JamesNZL/algovision/docs/Scopes/Power/Buck Converter.md

#5e5ce6/projects 

# Buck Converter

- Do I even need a buck converter, or should I just use a [[Low Dropout Regulator]]? I'm only going from $5\,\text{V}\to3.3\,\text{V}$...

- [Buck Regulators - Products (st.com)](https://www.st.com/en/power-management/buck-regulators/products.html)
- [Buck converters (integrated switch) product selection | TI.com](https://www.ti.com/power-management/non-isolated-dc-dc-switching-regulators/step-down-buck/buck-converter-integrated-switch/products.html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)
