JamesNZL/algovision/docs/Scopes/Software/Altium.md

#5e5ce6/projects 

# Altium Designer

- Used for the hardware schematic capture and PCB artwork design.

> [!note]
> I have also created my own schematic template with a custom title block.

![[Pasted image 20231009000126.png]]

![[Pasted image 20231120011738.png]]

![[Pasted image 20231120011808.png]]

![[Pasted image 20231009000355.png]]

![[Pasted image 20231009000413.png]]
