JamesNZL/algovision/docs/Scopes/Interface/User Pushbuttons.md

#5e5ce6/projects 

# User Pushbuttons

- [[Scopes/Interface/Reset Button]]

Also see [[Operating Modes]]
