JamesNZL/algovision/docs/Scopes/Power/Power Indicator.md

#5e5ce6/projects 

# Power Indicator

I want a power indication LED that can also communicate whether [[USB Power Delivery]] negotiation was successful.
