JamesNZL/algovision/docs/Scopes/Power/Input Protection.md

#5e5ce6/projects 

# Input Protection

> [!todo]
> https://www.st.com/resource/en/data_brief/tcpp01-m12.pdf
> [USB Type-C® protection and filtering - Application note (st.com)](https://www.st.com/resource/en/application_note/an4871-usb-typec-protection-and-filtering-stmicroelectronics.pdf)
