JamesNZL/algovision/docs/Scopes/Power/UCPD.md

#5e5ce6/projects 

# UCPD

> [!summary]
> What ST calls a [USB Type-C Power Delivery peripheral](https://wiki.st.com/stm32mcu/wiki/Introduction_to_USB_Power_Delivery_with_STM32).

Implements a [[USB-C Configuration Controller]] and a [[USB Power Delivery Control Peripheral]].
