JamesNZL/algovision/docs/Scopes/Power/Auto-Shutdown.md

#5e5ce6/projects 

# Auto-Shutdown

- MOSFET [[Load Switch]] circuit
- Can this be done with a latch instead?
	- Latch on button press, use micro to write reset—this might actually be more reliable?
	- How would the latch be powered when the circuit is first turned on?
