JamesNZL/algovision/docs/Scopes/Interface/Brightness Control.md

#5e5ce6/projects 

# Brightness Control

> [!todo]

- A potentiometer/rotary encoder for a brightness control knob?
- A light sensor?
- Both? Light sensor to automatically adjust, but knob to override?
- [Add ambient light sensor · Issue #31 · JamesNZL/algovision (github.com)](https://github.com/JamesNZL/algovision/issues/31)
