JamesNZL/algovision/docs/Scopes/Power/Boost Converter.md

#5e5ce6/projects 

# Boost Converter

> [!question]
> Is this necessary to drive the LEDs?

> [!fail] Not Needed
> No, if I create a [[Discrete LED Matrix]] with my own [[Discrete Non-Addressable RGB LEDs]] and [[LED Drivers]], I will not need to derive any higher voltage supply like I would if I were using a $12\,\text{V}$ module/panel or some other display.
