JamesNZL/algovision/docs/Scopes/Power/Battery Voltage Sensing.md

#5e5ce6/projects 

# Battery Voltage Sensing

> [!fail] Not Needed
> This is not needed if I use a [[USB Power Delivery]]—even if [[Batteries|battery]] powered using a power bank, the battery level would be displayed on the power bank itself, and I can rely on the negotiated nominal output voltage.
