JamesNZL/algovision/docs/Scopes/Firmware/Watchdog Timer.md

#5e5ce6/projects 

# Watchdog Timer

I want to add a watchdog timer to automatically reset if the system hangs.

Ideally, I want this to include a window watchdog (`WWDG`), such that I can use it to ensure, for example, that my row-control [[Shift Registers]] are being driven at the correct frequency.
