JamesNZL/algovision/docs/Scopes/Micro/Data Connector.md

#5e5ce6/projects 

# Data Connector

In complement to the [[Power Connector]], I want a dedicated data connector that I can use to flash/debug the [[Microcontroller]], such that I do not need the USB host (eg my laptop) to be capable (or expected) to source all the required [[Power]] for my board.
