JamesNZL/algovision/docs/Scopes/Micro/USB.md

#5e5ce6/projects 

# USB

- [[USB Type-C Connectors]]
- [[Scopes/Micro/USB to Serial]]
