JamesNZL/algovision/docs/Scopes/Micro/Connectivity.md

#5e5ce6/projects 

# Connectivity

> [!todo]

I want to learn more about the various wireless/connectivity protocols/options available.

- [[Bluetooth]]
- [[IEEE 802.11]]
- [[IEEE 802.15.4]]
- [[LoRa]]
- [[Application Layers]]
