JamesNZL/algovision/docs/Scopes/Micro/IEEE 802.15.4.md

#5e5ce6/projects 

# `IEEE 802.15.4`

- [[Zigbee]]
- [[Thread]]
