JamesNZL/algovision/docs/Scopes/Interface/Heartbeat LED.md

#5e5ce6/projects 

# Heartbeat LED

- Hook up to the main loop, or some other metric of activity/speed
