JamesNZL/algovision/docs/Scopes/Micro/Programming.md

#5e5ce6/projects 

# Programming

> [!todo]
> Need to research the various programming interfaces available, and determine which is most suitable.
> 
> Relevant Application Note: [Introduction to USB hardware and PCB guidelines using STM32 MCUs - Application note](https://www.st.com/resource/en/application_note/dm00296349-usb-hardware-and-pcb-guidelines-using-stm32-mcus-stmicroelectronics.pdf)

- [[SWD]]
- [[JTAG]]
- [[ISP]]
