JamesNZL/algovision/docs/Scopes/Software/Figma.md

#5e5ce6/projects 

# Figma

- Used to mock-up and design the matrix topology.

- Creating a re-usable LED component with a transparent 'lens', so I can duplicate it in a grid to produce a matrix, and 'display' an image through the lens
	![[Pasted image 20231008235531.png]]

![[Pasted image 20231008235513.png]]

![[Pasted image 20231008235622.png]]
