JamesNZL/algovision/docs/Scopes/Algorithms/Pathfinding.md

#5e5ce6/projects 

# Pathfinding Algorithms

- [[Scopes/Algorithms/Maze Generation]] should be pseudorandom
	- Floating ADC pin?
	- Linear feedback shift register?

1. [[Scopes/Algorithms/BFS]]
2. [[Scopes/Algorithms/DFS]]
3. [[Scopes/Algorithms/Dijkstra's]]
4. [[Scopes/Algorithms/A*]]
5. [[Scopes/Algorithms/Greedy Best-First Search]]
