JamesNZL/algovision/docs/Scopes/Algorithms/Sorting.md

#5e5ce6/projects 

# Sorting Algorithms

1. [[Scopes/Algorithms/Selection Sort]]
2. [[Scopes/Algorithms/Insertion Sort]]
3. [[Scopes/Algorithms/Bubble Sort]]
4. [[Scopes/Algorithms/Quick Sort]]
5. [[Scopes/Algorithms/Merge Sort]]
6. [[Scopes/Algorithms/Heap Sort]]
