JamesNZL/algovision/docs/Scopes/Display/Auto Display Repeat.md

#5e5ce6/projects 

# Auto Display Repeat

> [!quote] Datasheet Description
> - When disabled, each output driver is turned on and off once after `XBLNK` goes `HIGH`
> - When enabled, each output driver is repeatedly toggled on and off

> [!check] Enabled
> - Yes, I do want this, as I want each row to continue being displayed once the PWM counter overflows until I multiplex to the next row
