JamesNZL/algovision/docs/Scopes/Display/Dot Matrix Module.md

#5e5ce6/projects 

# Dot Matrix Module

Dot Matrix Module

| Part Number | `TS0230` |
| --- | --- |
| Image |  |
| Supplier Link | [DigiKey](https://www.digikey.com/en/products/detail/sunfounder/TS0230/16612468) |
| LED part | - |
| Resolution | 64 LEDs, $8\times 8$ matrix |
| Dimensions | $80\,\text{mm} \times 70\,\text{mm} \times 25\,\text{mm}$ |
| Operating Voltage | $5\,\text{V}$ |
| Max Current Draw  | Unknown |
| Driving Method | I2C |
| Data Lines | Unknown, necessarily $\geq 2$ |
| Cost | USD$26.85 |
| Remarks | No datasheet |

### Pros

- Can daisy chain together
- Is a developed module—less need for heat considerations etc
- No need to implement own driver circuitry

### Cons

- Effectively the same as buying a standard LED matrix
- Larger physical footprint
- Likely more expensive than buying the LEDs myself
