JamesNZL/algovision/docs/Scopes/Display/LCD Module.md

#5e5ce6/projects 

# LCD Module

LCD Module

### Pros

- Cheap

### Cons

- Can only easily display letters
- Must fit to each segment—would not work for the maze/logo
- Single colour
