JamesNZL/algovision/docs/Scopes/Display/LED Matrix Module.md

#5e5ce6/projects 

# LED Matrix Module

LED Matrix Panel

| Part Number | `Adafruit 420` | `Adafruit 607` |
| --- | --- | --- |
| Image |  |  |
| Supplier Link | [Adafruit](https://www.adafruit.com/product/420) | [Adafruit](https://www.adafruit.com/product/607) |
| LED part | `SMD3528` | |
| Resolution | 512 LEDs, $16\times 32$ matrix | 1024 LEDs, $32\times 32$ matrix |
| Dimensions | $192\,\text{mm} \times 96\,\text{mm} \times 12\,\text{mm}$ | $128\,\text{mm} \times 128\,\text{mm} \times 17\,\text{mm}$ |
| Operating Voltage | Regulated $5\,\text{V}$ | Regulated $5\,\text{V}$ |
| Max Current Draw  | $2.5\,\text{A}$ | $4\,\text{A}$ |
| Driving Method | $1/8$ scan, $50\sim60\,\text{Hz}$ | $1/16$ scan |
| Data Lines | 13 GPIO pins | 13 GPIO pins |
| Cost | USD$24.95 | USD$29.95 |
| Remarks | | |

### Pros

- Primarily the same as that for a custom-built LED matrix with discrete LEDs
- Probably cheaper than building it myself

### Cons
- Don't get to do the design/layout myself
