JamesNZL/algovision/docs/Scopes/Display/OLED Module.md

#5e5ce6/projects 

# OLED Module

OLED Module

### Pros

- Less power draw
- Lighter, thinner
- Higher resolution/pixel density

### Cons

- Small—hard to read
- Can get expensive for larger screens/higher resolutions
- Doesn't look very good, in my opinion
