JamesNZL/algovision/docs/Scopes/Display/TFT Display.md

#5e5ce6/projects 

# TFT Display

TFT Display Module

### Pros

- Highest resolution?
- Easier to get in larger sizes than OLED modules
- More cost effective

### Cons

- Scope creep?
- Small physical size
- Not as 'interesting' as an LED matrix?
- Requires a backlight—higher power draw
