JamesNZL/algovision/docs/Scopes/Display/Uniformity.md

#5e5ce6/projects 

# Uniformity

> [!question]
> What is the current ratio of `R`/`G`/`B` for the best uniformity?
> What should I set the `DC` Dot Correction bits to?

`9.4.2`

> [!todo] Uniformity Dot Correction
> Select the `DC` data for the best uniformity of the RGB channels and write the data with other control data.
