JamesNZL/algovision/docs/Scopes/Display/White Balance.md

#5e5ce6/projects 

# White Balance

> [!question]
> What is the current ratio of `R`/`G`/`B` for the best white balance?
> What should I set the `BC` Global Brightness Control bits to?

`9.4.3`

> [!todo] White Balance Global Brightness Control
> Select the `BC` data for the best white balance of the RGB channels and write the data with other control data.
