JamesNZL/algovision/docs/Scopes/Display/Discrete Non-Addressable RGB LEDs.md

#5e5ce6/projects 

# Discrete Non-Addressable RGB LEDs

| Part Number | `CLMVC-FKA-CL1D1L71BB7C3C3` | `IN-S66TBTRGB` | `IN-P32TATRGB` | `150141M173100` | `IN-S128TATRGB` | `ASMB-LTB2-0A333` | `ASMB-KTF0-0A306` | `LTST-C19HE1WT` | `ASMB-TTF0-0A20B` |
| --- | --- | --- | --- | --- | --- | --- | --- | --- | --- |
| Image |  |  |  |  |  |  |  |  |  |
| Supplier Link | [DigiKey](https://www.digikey.com/en/products/detail/creeled-inc/CLMVC-FKA-CL1D1L71BB7C3C3/4794065) | [DigiKey]([DigiKey](https://www.digikey.com/en/products/detail/inolux/IN-S66TBTRGB/7604944)) | [DigiKey]([DigiKey](https://www.digikey.com/en/products/detail/inolux/IN-P32TATRGB/7604884)) | [DigiKey](https://www.digikey.com/en/products/detail/w%C3%BCrth-elektronik/150141M173100/4489960) | [DigiKey](https://www.digikey.com/en/products/detail/inolux/IN-S128TATRGB/7604911) | [DigiKey](https://www.digikey.com/en/products/detail/broadcom-limited/ASMB-LTB2-0A333/9740374) | [DigiKey](https://www.digikey.com/en/products/detail/broadcom-limited/ASMB-KTF0-0A306/7915692) | [DigiKey](https://www.digikey.com/en/products/detail/liteon/LTST-C19HE1WT/3198710) | [DigiKey](https://www.digikey.com/en/products/detail/broadcom-limited/ASMB-TTF0-0A20B/7915694) |
| Colour | RGB | RGB | RGB | RGB | RGB | RGB | RGB | RGB | RGB |
| Lens | Clear | Clear | Clear | Clear | Clear | Diffused | Diffused | Diffused | Diffused |
| Package/Dimensions | $2\,\text{mm} \times 2\,\text{mm} \times 1\,\text{mm}$ | $1.6\,\text{mm} \times 1.5\,\text{mm} \times 0.55\,\text{mm}$ | $3.5\,\text{mm} \times 2.8\,\text{mm} \times 1.9\,\text{mm}$ | $3.5\,\text{mm} \times 2.8\,\text{mm} \times 1.9\,\text{mm}$ | $3.2\,\text{mm} \times 2.7\,\text{mm} \times 1.1\,\text{mm}$ | $2.1\,\text{mm} \times 2.1\,\text{mm} \times 1\,\text{mm}$ | $2.2\,\text{mm} \times 2\,\text{mm} \times 1.9\,\text{mm}$ | $1.6\,\text{mm} \times 1.6\,\text{mm} \times 0.35\,\text{mm}$ | $3.7\,\text{mm} \times 3.5\,\text{mm} \times 2.8\,\text{mm}$ |
| Absolute Maximum Voltage | $3.7\,\text{V}$ | $3.6\,\text{V}$ | $3.6\,\text{V}$ | $3.6\,\text{V}$ | $3.6\,\text{V}$ | $3.4\,\text{V}$ | $3.3\,\text{V}$ | $3.9\,\text{V}$ | $3.6\,\text{V}$ |
| Average Forward Current  | $51\,\text{mA}$ | $75\,\text{mA}$ | $90\,\text{mA}$ | $90\,\text{mA}$ | $75\,\text{mA}$ | $55\,\text{mA}$ | $60\,\text{mA}$ | $70\,\text{mA}$ | $110\,\text{mA}$ |
| Frequency | - | - | - | - | - | - | - | - | - |
| Configuration | Common anode | Common anode | Common anode | Common anode | Common anode | Common anode | Common anode | Common anode | Direct connection to A/K |
| Data Lines | $\geq 3$ GPIO pins | $\geq 3$ GPIO pins | $\geq 3$ GPIO pins | $\geq 3$ GPIO pins | $\geq 3$ GPIO pins | $\geq 3$ GPIO pins | $\geq 3$ GPIO pins | $\geq 3$ GPIO pins | $\geq 3$ GPIO pins |
| Cost (for 256) | USD$50.20 | USD$41.63 | USD$44.60 | USD$109.06 | USD$47.56 | USD$65.05 | USD$41.63 | USD$46.80 | USD$55.91 |
| Remarks | | | | | | | Designed specifically for a fine pitch | | |

- For these non-addressable LEDs, it will be much more difficult to get a specific colour value as I will need to produce the PWM signals myself—which would likely be incredibly complex for a matrix
	- ie, I will need to produce the PWM signal for the RGB data lines for each of my LEDs at the output of my shift register, if I want to have more than just the base combination of colours
	- This is $3\times n_\text{LEDs}$ bits per row, where $n_\text{LEDs}$ is the number of LEDs in that row
	- I will also need to refresh each row *multiple (many)* times per display state, in order to produce the necessary PWM for each of the RGB data lines
	- This is likely to become impracticable for a large matrix—I would need to refresh each row *multiple (many)* times per display state, in order to produce the necessary PWM for each of the RGB data lines
	- This is likely to become impracticable, as I would need to refresh each row 256 times per frame to produce the typical 16.8 M colours (ie giving each RGB data line a PWM duty cycle of 256 'counts')
	- Thus to drive the display at a reasonable $30\,\text{fps}$, the timing requirements are likely to become quite complex & computationally disruptive (many interrupts very quickly)
	- It would also likely be reasonably complex to implement correctly
	- Would also produce a worse colour output as there is no constant current drive circuity; each RGB data input would require its own current limiting protection resistor, etc
	- Could use an LED driver IC to resolve most of those problems, but DigiKey only stocks ICs with up to 48 outputs—this would correspond to only 16 RGB LEDs per driver, requiring *lots* of drivers for a full matrix—accounting for GPIO pins/routing paths (not to mention cost), this is still not very practicable

> [!question]
> I'm actually not convinced by this... people have built $8\times 8\times 8 = 512$ RGB LED cubes with non-addressable LEDs, so it must be possible and realistic

- Addressing the hardware concerns—if I employ both shifting (standard shift registers or LED drivers) and multiplexing, I am sure I can significantly cut down on the number of ICs required—it would just increase the complexity of the firmware, but that is fine, provided the clock timing requirements remain reasonable
	- If I want to drive 8 LEDs at once, this requires $8\times 3 = 24\,\text{bits}$ required in the shift register, or 24 channels in the LED driver
	- If I use a 48 channel LED driver, this would correspond to 16 LEDs at once
	- Assuming a matrix of $20\times 16$, this could be one entire column at once
	- I could then use a single driver and multiplex through the columns one at a time
	- This would be very reasonable...
	- With two drivers, I could scan through from Column 0 to Column 9 and Column 10 to Column 19, which I have seen detailed in the datasheets for the Adafruit matrices as providing a smoother visual appearance
 
| Part Number | `NH-B1212RGBA-HF` | `NH-B1515RGBA-HF` | `NH-B2020RGBA-HF` | `RS-1515MBAM` | `MHPA2121URGBDT` | `ASCB-JTC2-0A308` |
| --- | --- | --- | --- | --- | --- | --- |
| Image |  |  |  |  |  |  |
| Supplier Link | [LCSC](https://www.lcsc.com/product-detail/Light-Emitting-Diodes-LED_Foshan-NationStar-Optoelectronics-NH-B1212RGBA-HF_C2874114.html) | [LCSC](https://www.lcsc.com/product-detail/Light-Emitting-Diodes-LED_Foshan-NationStar-Optoelectronics-NH-B1515RGBA-HF_C2874115.html) | [LCSC](https://www.lcsc.com/product-detail/Light-Emitting-Diodes-LED_Foshan-NationStar-Optoelectronics-NH-B2020RGBA-HF_C2874116.html) | [LCSC](https://www.lcsc.com/product-detail/Light-Emitting-Diodes-LED_Foshan-NationStar-Optoelectronics-RS-1515MBAM_C727906.html) | [LCSC](https://www.lcsc.com/product-detail/Light-Emitting-Diodes-LED_MEIHUA-MHPA2121URGBDT_C404284.html) | [DigiKey](https://www.digikey.com/en/products/detail/broadcom-limited/ASCB-JTC2-0A308/15181480) |
| Colour | RGB | RGB | RGB | RGB | RGB | RGB |
| Lens | Diffused square | Diffused square | Diffused circle | Diffused square | Diffused circle | Diffused square |
| Package/Dimensions | $1.23\,\text{mm} \times 1.2\,\text{mm} \times 0.9\,\text{mm}$ | $1.6\,\text{mm} \times 1.5\,\text{mm} \times 1\,\text{mm}$ | $2.1\,\text{mm} \times 2.1\,\text{mm} \times 1\,\text{mm}$ | $1.6\,\text{mm} \times 1.5\,\text{mm} \times 1\,\text{mm}$ | $2.1\,\text{mm} \times 2.1\,\text{mm} \times 1\,\text{mm}$ | $1.6\,\text{mm} \times 1.5\,\text{mm} \times 1\,\text{mm}$ |
| Absolute Maximum Voltage | $3.2\,\text{V}$ | $3.2\,\text{V}$ | $3.2\,\text{V}$ | $3.4\,\text{V}$ | $3.1\,\text{V}$ | $3.1\,\text{V}$ |
| Average Forward Current  | $60\,\text{mA}$ | $60\,\text{mA}$ | $60\,\text{mA}$ | $50\,\text{mA}$ | $65\,\text{mA}$ | $46\,\text{mA}$ |
| Configuration | Common anode | Common anode | Common anode | Common anode | Common anode | Common anode |
| Data Lines | $\geq 3$ GPIO pins | $\geq 3$ GPIO pins | $\geq 3$ GPIO pins | $\geq 3$ GPIO pins | $\geq 3$ GPIO pins | $\geq 3$ GPIO pins |
| Cost (for 256) | USD2.44 | USD$1.98 | USD$1.98 | USD$4.47 | USD$15.76 | USD$71.71 |
| Remarks | | | | | | |

As commented above an in [[Discrete Addressable LEDs]], these devices are the ones that I think will look the best package-wise on my board, as I can find them in a black colour and with diffused lenses, both of which I am unable to find with addressable LEDs.

> [!success] Preferred Device(s)
>  If I choose to go with non-addressable LEDs, I would select:
> 1. [`RS-1515MBAM`](https://www.lcsc.com/product-detail/Light-Emitting-Diodes-LED_Foshan-NationStar-Optoelectronics-RS-1515MBAM_C727906.html), for price, lens, and forward current.
> 2. [`NH-B1515RGBA-HF`](https://www.lcsc.com/product-detail/Light-Emitting-Diodes-LED_Foshan-NationStar-Optoelectronics-NH-B1515RGBA-HF_C2874115.html) as it is pin compatible.
> 3. [`ASCB-JTC2-0A308`](https://www.digikey.com/en/products/detail/broadcom-limited/ASCB-JTC2-0A308/15181480) as it is pin compatible.
> 4. [`CLMVC-FKA-CL1D1L71BB7C3C3`](https://www.digikey.com/en/products/detail/creeled-inc/CLMVC-FKA-CL1D1L71BB7C3C3/4794065).
