JamesNZL/algovision/docs/Scopes/Assets/Fonts.md

#5e5ce6/projects 

# Fonts

> [!summary]
> The [`Karbon`](https://klim.co.nz/retail-fonts/karbon/) font family is licensed for perpetual use within this project under the terms of the [Klim Desktop Font Licence Agreement](https://klim.co.nz/licences/desktop-fonts/).

After evaluating a shortlist of different fonts from a number of different font foundaries, I have [[Scopes/Assets/Font Selection|selected]] the `Karbon` font family from the Klim Type Foundry.

## Styles Used

1. Karbon Regular
2. Karbon Semibold
3. Karbon Bold

- [[Illustrator]]

| Component | Style |
| --- | --- |
| Logomark  | 2 — Karbon Semibold |
| Wordmark  | 3 — Karbon Bold | 

- [[Figma]]

| Component | Style |
| --- | --- |
| Annotations | 1 — Karbon Regular | 

- [[Altium]]

**Schematics**

| Component | Style |
| --- | --- |
| Text | 1 — Karbon Regular  |
| Title Block | 1 — Karbon Regular  |
| Title Block | 2 — Karbon Semibold |
| Title Block | 3 — Karbon Bold |

**Artwork**

*Test Board*

| Component | Style |
| --- | ----- |
| Reference Designators | 3 — Karbon Bold |
