JamesNZL/algovision/docs/Scopes/Display/Discrete Addressable LEDs.md

#5e5ce6/projects 

# Discrete Addressable LEDs

| Part Number | `601000200` | `IN-PI15TAT5R5G5B` | `IN-PI20TBT5R5G5B` | `IN-PI22TAT5R5G5B` | `T3A33BRG-H9C0002X1U1930` | `FZ2812-5050` | `IN-PI554FCH` | `IN-PI55QATPRPGPBPW-40` | `IN-PC55TBTRGB` | `LTST-E263CEGBK` | `19-C47/RSGHBHC-5V01/2T` | `WS2812B-B/T` | `DY-S1515065/RGBC/6805-5T` | `SK6805-EC15` | `SK6805-EC20` |
| --- | --- | --- | --- | --- | --- | --- | --- | --- | --- | --- | --- | --- | --- | --- | --- |
| Image |  |  |  |  |  |  |  |  |  |  |  |  |  |  |  |
| Supplier Link | [DigiKey](https://www.digikey.com/en/products/detail/seeed-technology-co-ltd/601000200/8120706) | [DigiKey](https://www.digikey.co.nz/en/products/detail/inolux/IN-PI15TAT5R5G5B/14555725) | [DigiKey](https://www.digikey.co.nz/en/products/detail/inolux/IN-PI20TBT5R5G5B/14555723) | [DigiKey](https://www.digikey.co.nz/en/products/detail/inolux/IN-PI22TAT5R5G5B/9681237) | [DigiKey](https://www.digikey.co.nz/en/products/detail/harvatek-corporation/T3A33BRG-H9C0002X1U1930/15930508)  | [DigiKey](https://www.digikey.co.nz/en/products/detail/feztek/FZ2812-5050/18647407) | [DigiKey](https://www.digikey.co.nz/en/products/detail/inolux/IN-PI554FCH/7604874) | [DigiKey](https://www.digikey.co.nz/en/products/detail/inolux/IN-PI55QATPRPGPBPW-40/9681240) | [DigiKey](https://www.digikey.co.nz/en/products/detail/inolux/IN-PC55TBTRGB/9681242) | [DigiKey](https://www.digikey.co.nz/en/products/detail/liteon/LTST-E263CEGBK/9556405) | [DigiKey](https://www.digikey.co.nz/en/products/detail/everlight-electronics-co-ltd/19-C47-RSGHBHC-5V01-2T/9962978) | [LCSC](https://www.lcsc.com/product-detail/Light-Emitting-Diodes-LED_Worldsemi-WS2812B-B-T_C2761795.html) | [LCSC](https://www.lcsc.com/product-detail/Light-Emitting-Diodes-LED_TONYU-DY-S1515065-RGBC-6805-5T_C524053.html) | [LCSC](https://www.lcsc.com/product-detail/Light-Emitting-Diodes-LED_OPSCO-Optoelectronics-SK6805-EC15_C2890035.html) | [LCSC](https://www.lcsc.com/product-detail/Light-Emitting-Diodes-LED_OPSCO-Optoelectronics-SK6805-EC20_C2890036.html) |
| Colour | RGB | RGB | RGB | RGB | RGB | RGB | RGB | RGBW | RGB | RGB | RGB | RGB | RGB | RGB | RGB |
| Lens | Clear | Diffused | Diffused | Diffused | Clear | Clear | Clear | Diffused | Diffused | Clear | Clear | Diffused | Diffused | Clear | Clear |
| Package/Dimensions | $5.4\,\text{mm} \times 5\,\text{mm} \times 1.65\,\text{mm}$ | $1.5\,\text{mm} \times 1.5\,\text{mm} \times 0.65\,\text{mm}$ | $2\,\text{mm} \times 2\,\text{mm} \times 0.65\,\text{mm}$ | $2.7\,\text{mm} \times 2.4\,\text{mm} \times 1.1\,\text{mm}$ | $5.36\,\text{mm} \times 5\,\text{mm} \times 1.6\,\text{mm}$ | $5\,\text{mm} \times 5\,\text{mm} \times 1.6\,\text{mm}$ | $5\,\text{mm} \times 5\,\text{mm} \times 1.6\,\text{mm}$ | $5\,\text{mm} \times 5\,\text{mm} \times 1.6\,\text{mm}$ | $5\,\text{mm} \times 5\,\text{mm} \times 1.6\,\text{mm}$ | $1.8\,\text{mm} \times 1.8\,\text{mm} \times 0.65\,\text{mm}$ | $1.8\,\text{mm} \times 1.8\,\text{mm} \times 0.65\,\text{mm}$ | $5\,\text{mm} \times 5\,\text{mm} \times 1.6\,\text{mm}$ | $1.5\,\text{mm} \times 1.5\,\text{mm} \times 0.65\,\text{mm}$ | $1.5\,\text{mm} \times 1.5\,\text{mm} \times 0.65\,\text{mm}$ | $2\,\text{mm} \times 2\,\text{mm} \times 0.65\,\text{mm}$ |
| Power Supply Voltage | $3.7 \sim 5.3\,\text{V}$ | $3.7 \sim 5.5\,\text{V}$ | $3.7 \sim 5.5\,\text{V}$ | $3.5 \sim 5.5\,\text{V}$ | $3.3 \sim 5.5\,\text{V}$ | $3 \sim 7\,\text{V}$ | $3.5 \sim 5.5\,\text{V}$ | $3.5 \sim 5.5\,\text{V}$ | $5 \sim 5.3\,\text{V}$ | $3.8 \sim 5.5\,\text{V}$ | $4.2 \sim 5.5\,\text{V}$ | $3.7 \sim 5.3\,\text{V}$ | $3.7 \sim 5.5\,\text{V}$ | $3.7 \sim 5.5\,\text{V}$ | $3.7 \sim 5.5\,\text{V}$ |
| Average Forward Current | $48\,\text{mA}$ | $15\,\text{mA}$ | $15\,\text{mA}$ | $15\,\text{mA}$ | $30\,\text{mA}$ | $25\,\text{mA}$ | $36\,\text{mA}$ | $36\,\text{mA}$ | $60\,\text{mA}$ | $19\,\text{mA}$ | $15\,\text{mA}$ | $36\,\text{mA}$ | $15\,\text{mA}$ | $15\,\text{mA}$ | $15\,\text{mA}$ |
| PWM Frequency | $2\,\text{kHz}$ | $1.2\,\text{kHz}$ | $1.2\,\text{kHz}$ | $1.2\,\text{kHz}$ | | $2\,\text{kHz}$ | $1.2\,\text{kHz}$ | $1.2\,\text{kHz}$ | $1.2\,\text{kHz}$ | | | $2\,\text{kHz}$ | $1.2\,\text{kHz}$ | $1.2\,\text{kHz}$ | $1.2\,\text{kHz}$ |
| Data Frequency | $800\,\text{kHz}$ | $800\,\text{kHz}$ | $800\,\text{kHz}$ | $800\,\text{kHz}$ | $15\,\text{MHz}$ | $800\,\text{kHz}$ | $800\,\text{kHz}$ | $800\,\text{kHz}$ | $30\,\text{MHz}$ | $800\,\text{kHz}$ | | $800\,\text{kHz}$ | $800\,\text{kHz}$ | $800\,\text{kHz}$ | $80\,\text{kHz}$ |
| Protocol | 24bit serial GRB | 24bit serial GRB | 24bit serial GRB | 24bit serial GRB | 32bit serial BRG | 24bit serial GRB | 24bit serial GRB | 32bit serial GRBW | 32bit serial BGR | Unspecified | 24bit serial RGB | 24bit serial GRB | 24bit serial GRB | 24bit serial GRB | 24bit serial GRB |
| Data Lines | $\geq 1$ GPIO pin | 1 GPIO pin | 1 GPIO pin | 1 GPIO pin | 2 GPIO pins | 1 GPIO pin | 1 GPIO pin | 1 GPIO pin | 2 GPIO pins | 1 GPIO pin | 1 GPIO pin | 1 GPIO pin | 1 GPIO pin | 1 GPIO pin | 1 GPIO pin |
| Cost (for 256) | USD$58.37 | USD$58.88 | USD$58.88 | USD$75.06 | USD$64.00 | USD$72.27 | USD$78.59 | USD$78.59 | USD$78.59 | USD$98.25 | USD$98.25 | USD$16.41 | USD$22.41 | USD$34.92 | USD$38.22 |
| Remarks | Has internal decoupling capacitor | | | | | | | | Two-wire synchronous control | | | | | | |

> [!summary] Preferred Devices
> I would prefer the black `WS2812B-B/T` from LCSC over any of the white offerings from DigiKey due to colour/price considerations, *except* for possibly the `IN-PI15TAT5R5G5B` or the larger `IN-PI20TBT5R5G5B`—the price difference here isn't *that* extreme (compared to the comparable LCSC devices), and I would prefer to order from DigiKey due to shipping/order consolidation reasons. Also, the DigiKey devices are diffused, and the datasheets are in English.

> [!fail]
> But, I would actually prefer the all-black & black diffused LEDs that are available in a common anode configuration... these are also *considerably* cheaper from LCSC, eg USD\$3 vs USD\$30 for 256.
> Also, individually addressable LEDs might be *too easy*... in the sense that they might be a bit too straight-forward to drive, making this project too easy.
> Also, it'd mean that the board is effectively just the uC + LEDs + power, without needing anything other ICs for the matrix... I kind of want something more involved.
> I'll compare some more common anode/cathode RGB LEDs in the physical packages I'm after, and see if I can figure out a nice way to drive them all.
