JamesNZL/algovision/docs/images/Pasted image 20231107172127.png

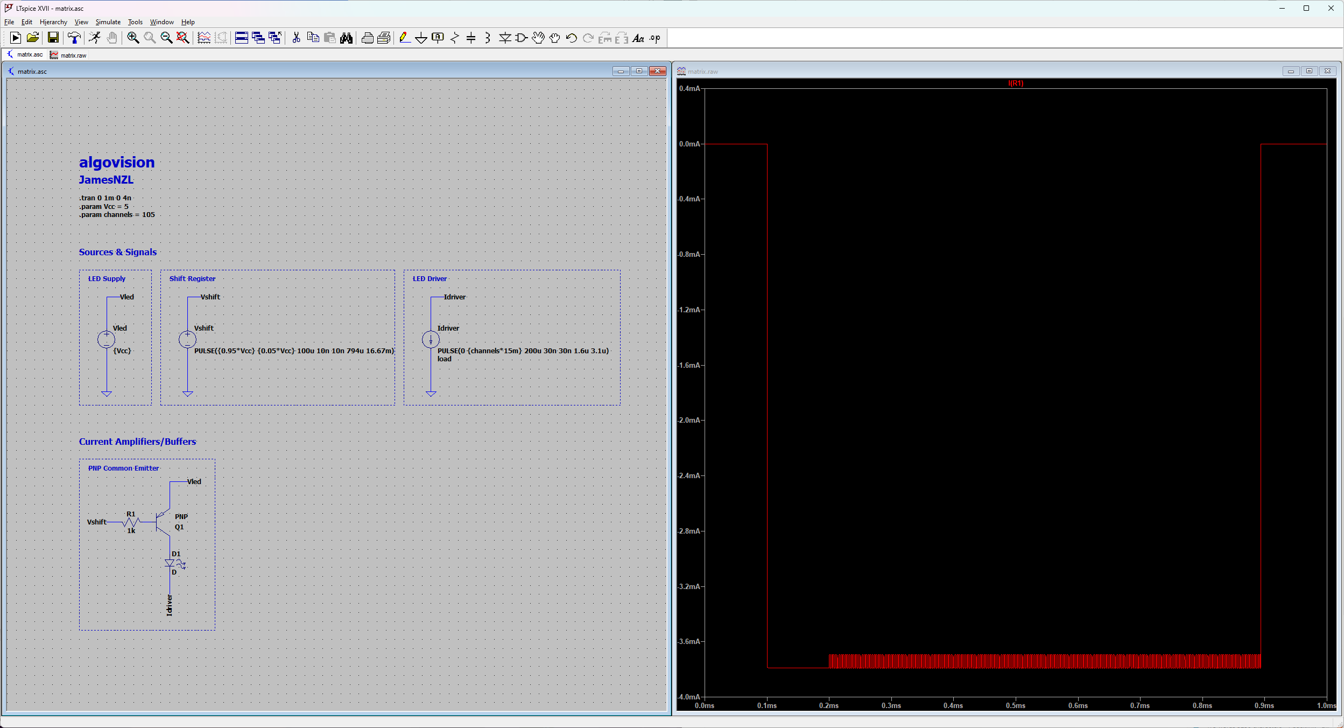
docs/images/Pasted image 20231107172127.png
