JamesNZL/algovision/docs/images/Pasted image 20231107190516.png

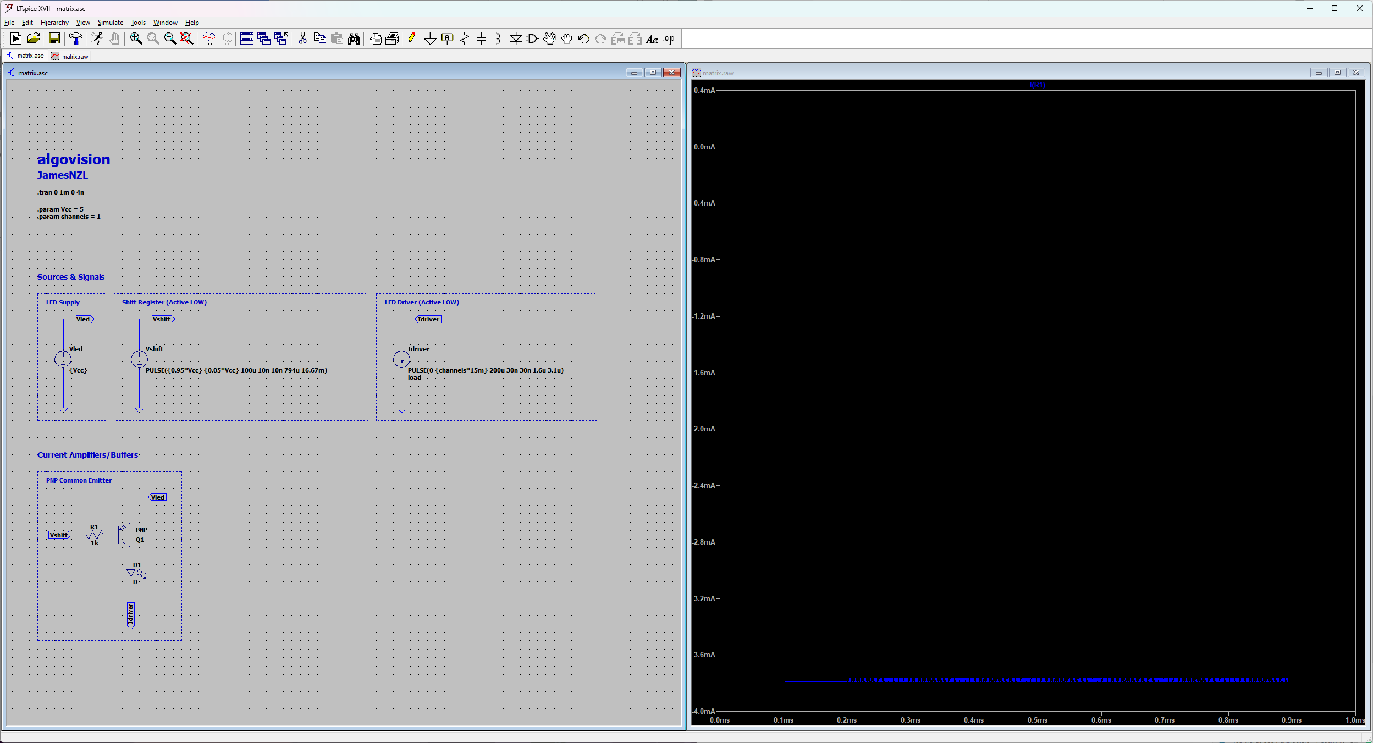
docs/images/Pasted image 20231107190516.png
