JamesNZL/algovision/docs/images/Pasted image 20231107200609.png

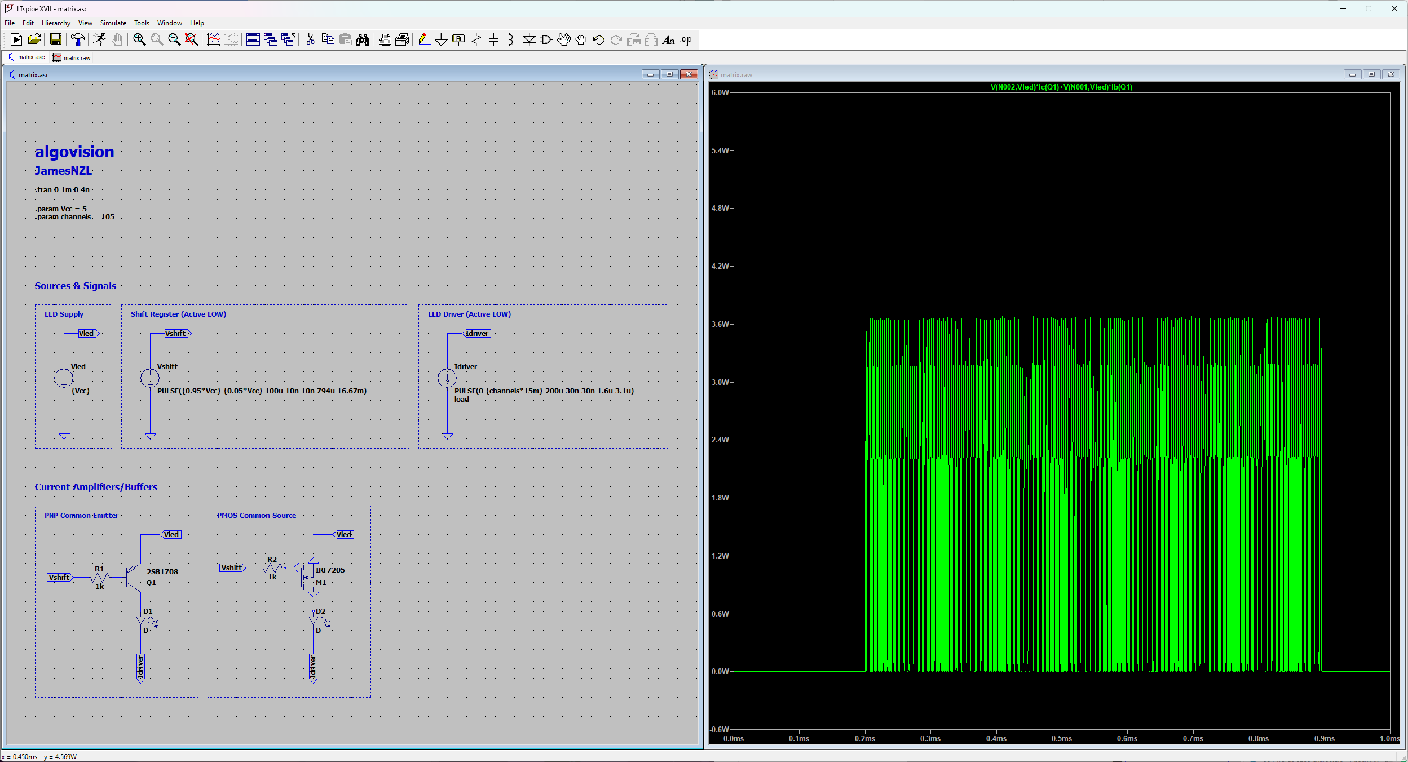
docs/images/Pasted image 20231107200609.png
