JamesNZL/algovision/docs/images/Pasted image 20231120213647.png

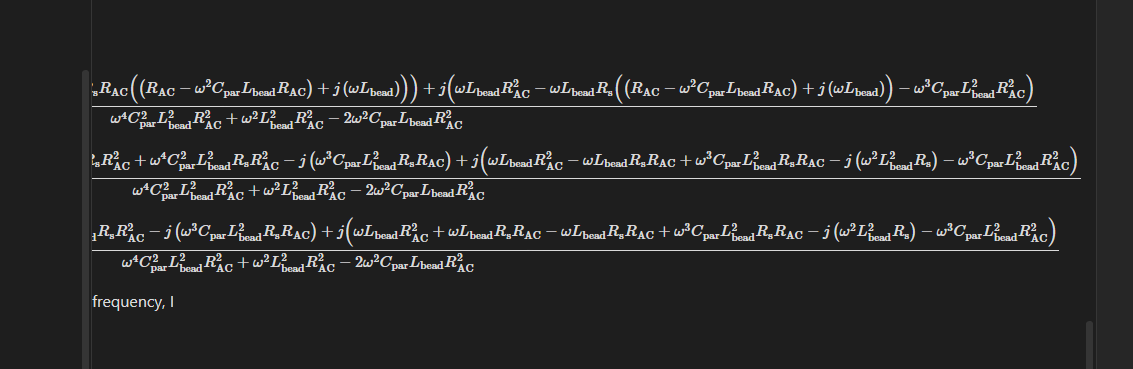
docs/images/Pasted image 20231120213647.png
