JamesNZL/algovision/docs/images/Pasted image 20231121012136.png

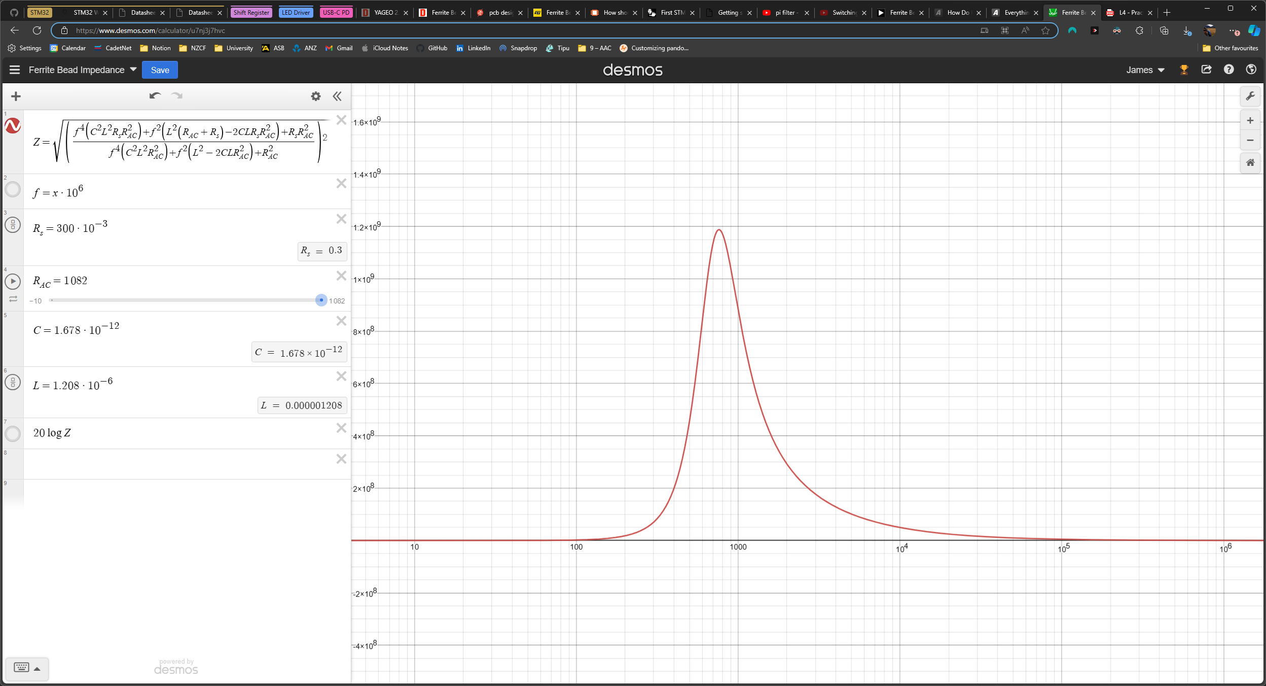
docs/images/Pasted image 20231121012136.png
