JamesNZL/algovision/docs/images/Pasted image 20231121131928.png

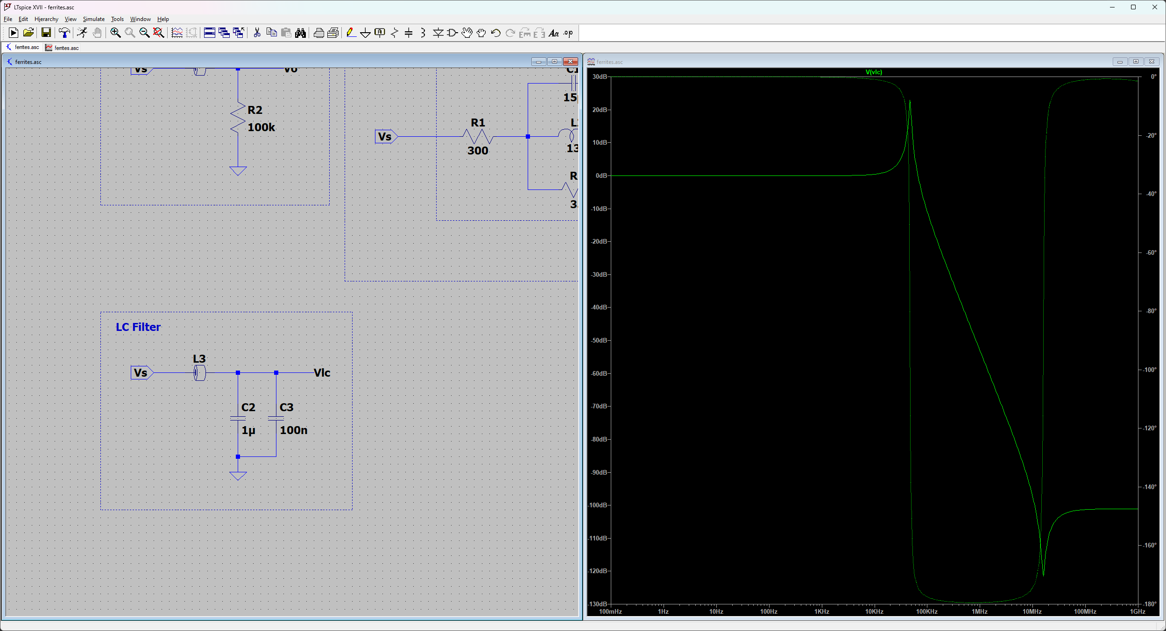
docs/images/Pasted image 20231121131928.png
