JamesNZL/algovision/docs/images/Pasted image 20231121132448.png

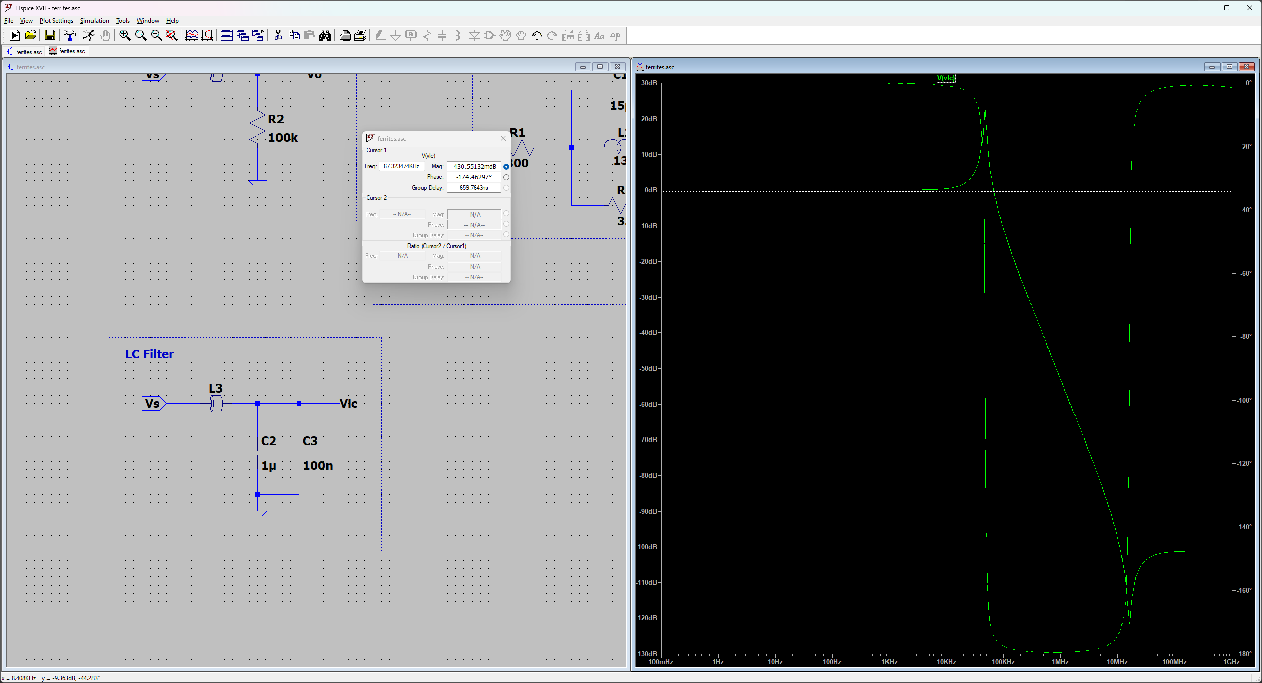
docs/images/Pasted image 20231121132448.png
