JamesNZL/algovision/docs/images/Pasted image 20231121134122.png

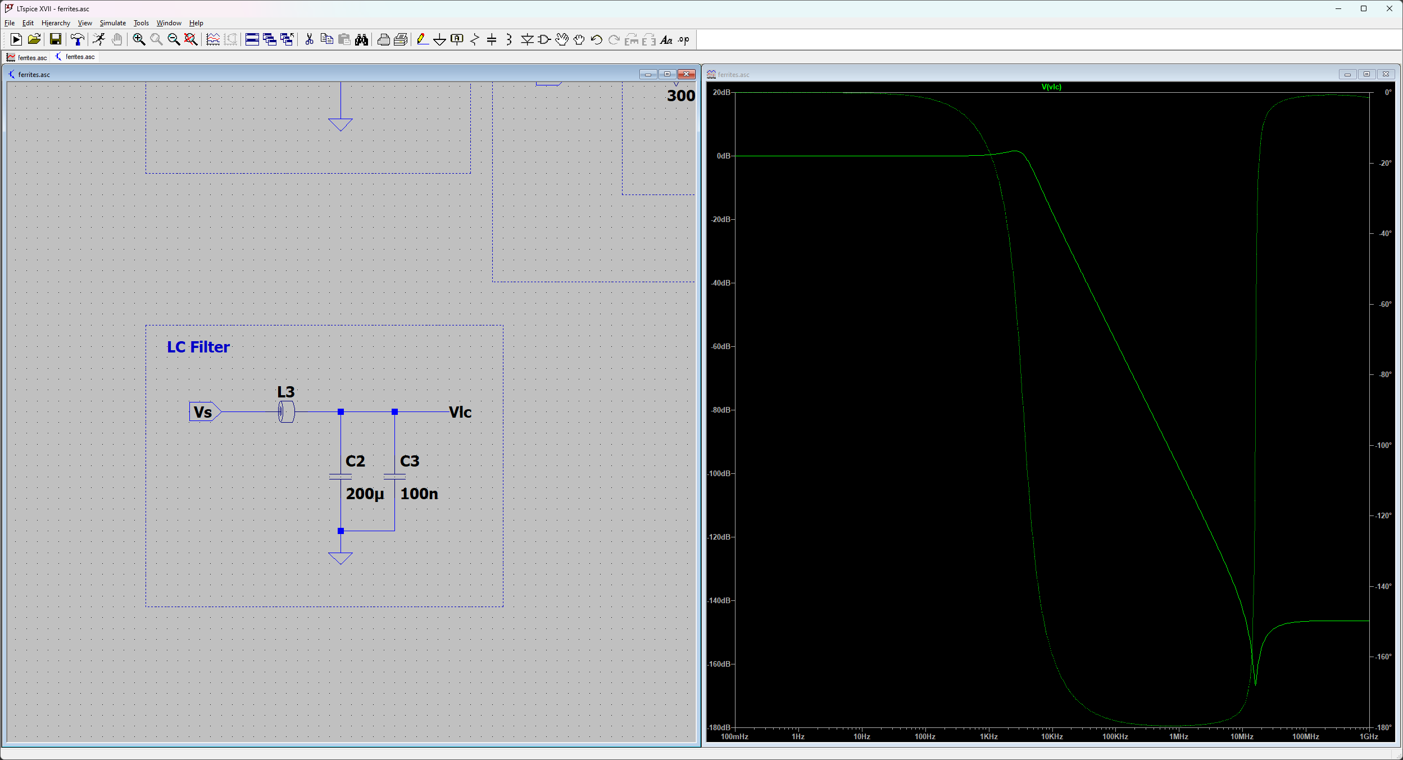
docs/images/Pasted image 20231121134122.png
