JamesNZL/algovision/docs/images/Pasted image 20231121134246.png

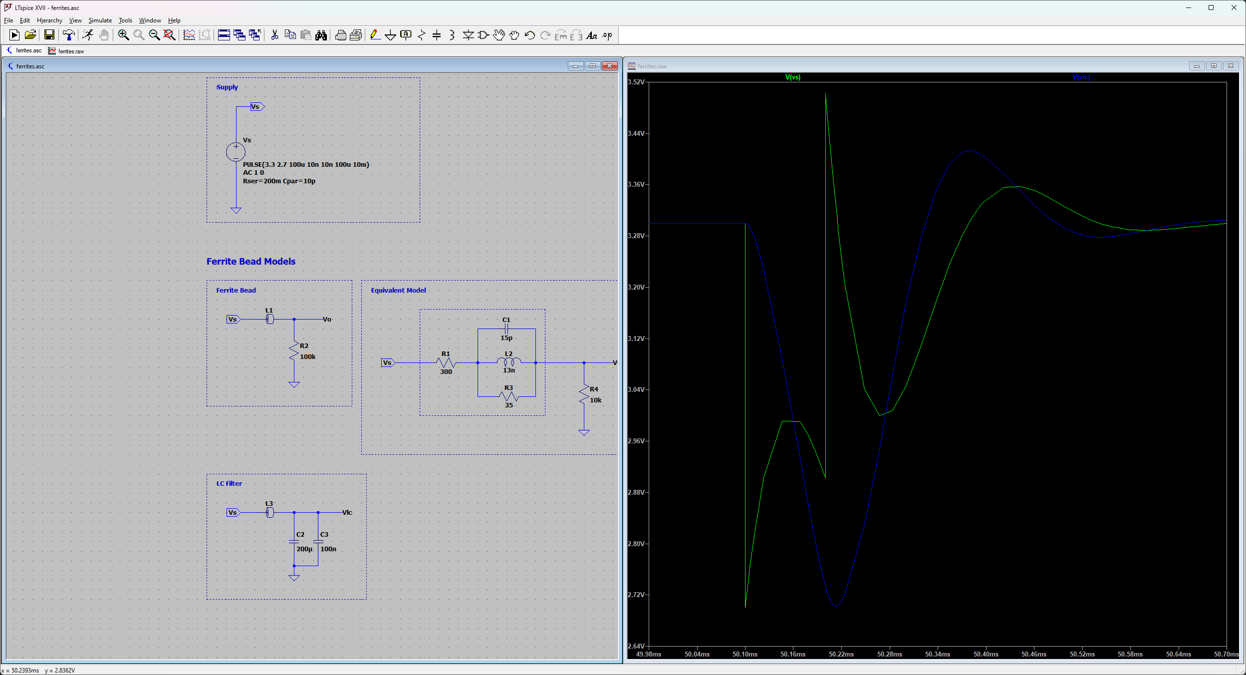
docs/images/Pasted image 20231121134246.png
