JamesNZL/algovision/docs/images/Pasted image 20231121165913.png

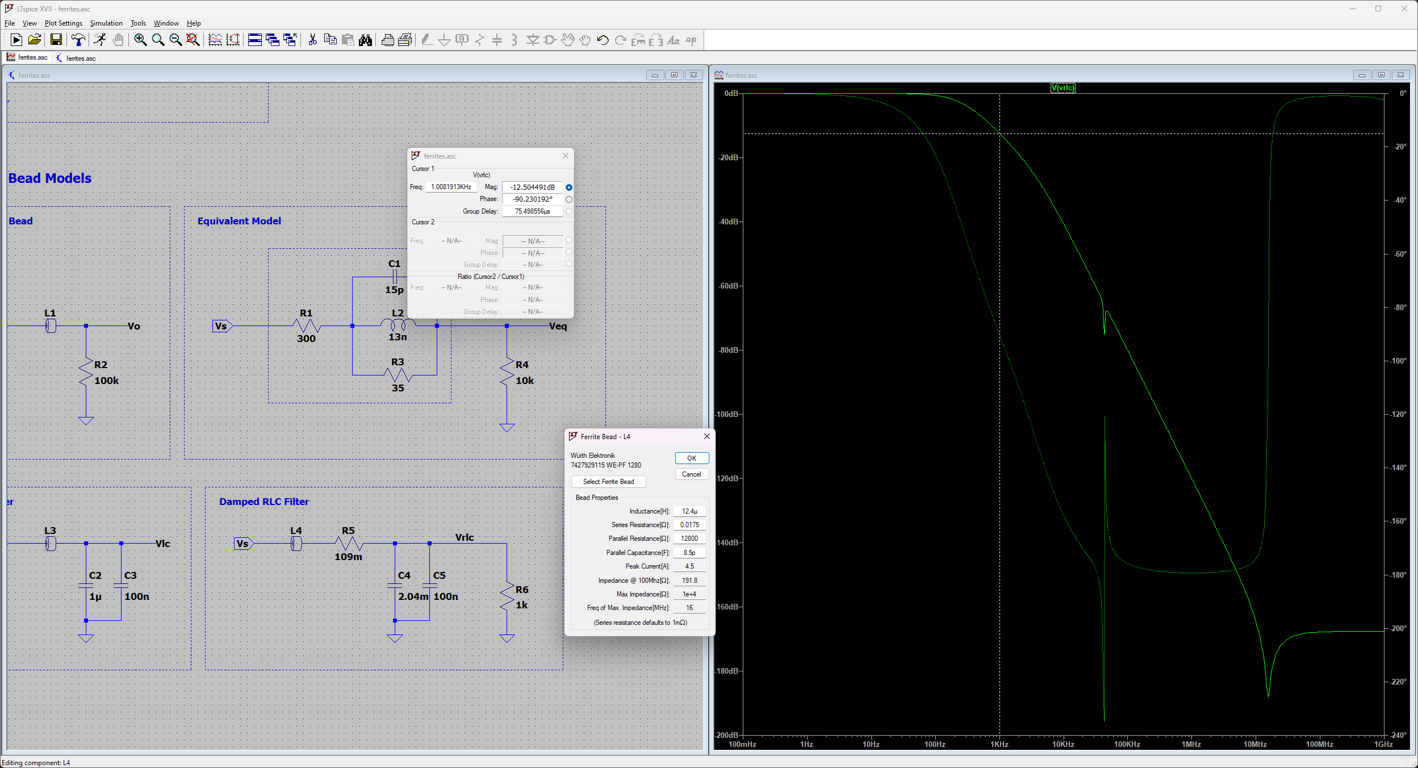
docs/images/Pasted image 20231121165913.png
