JamesNZL/algovision/docs/images/Pasted image 20231121170502.png

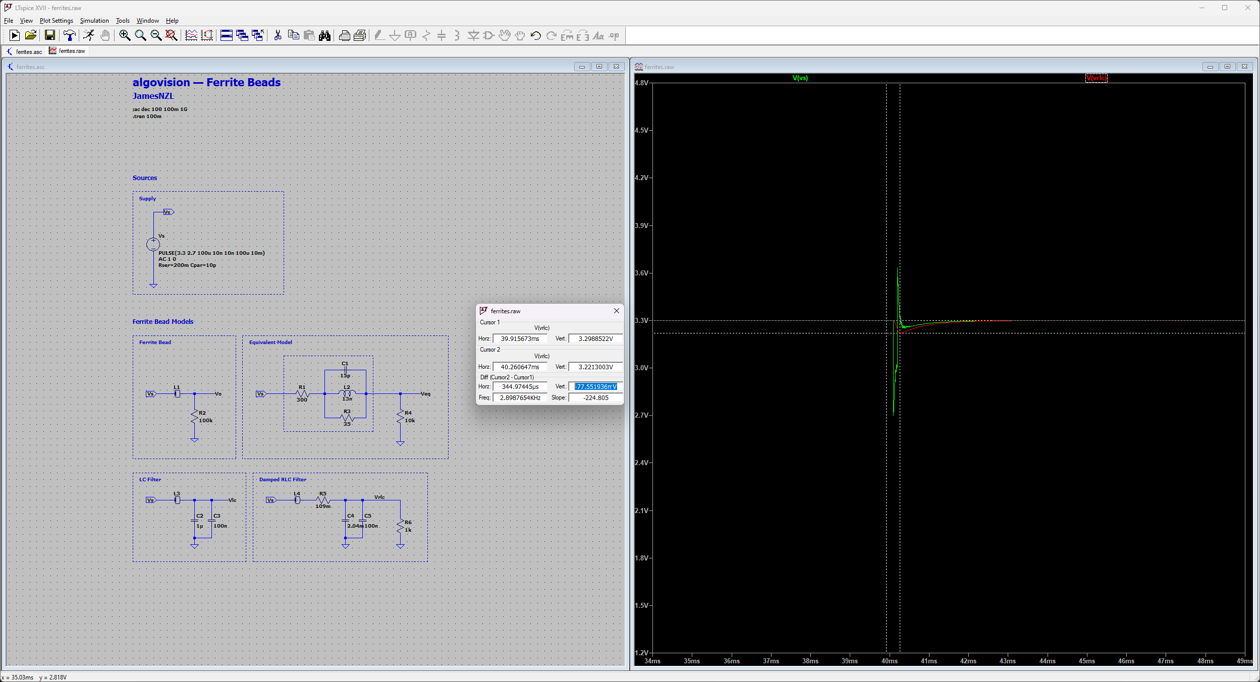
docs/images/Pasted image 20231121170502.png
