JamesNZL/algovision/docs/images/Pasted image 20231121190456.png

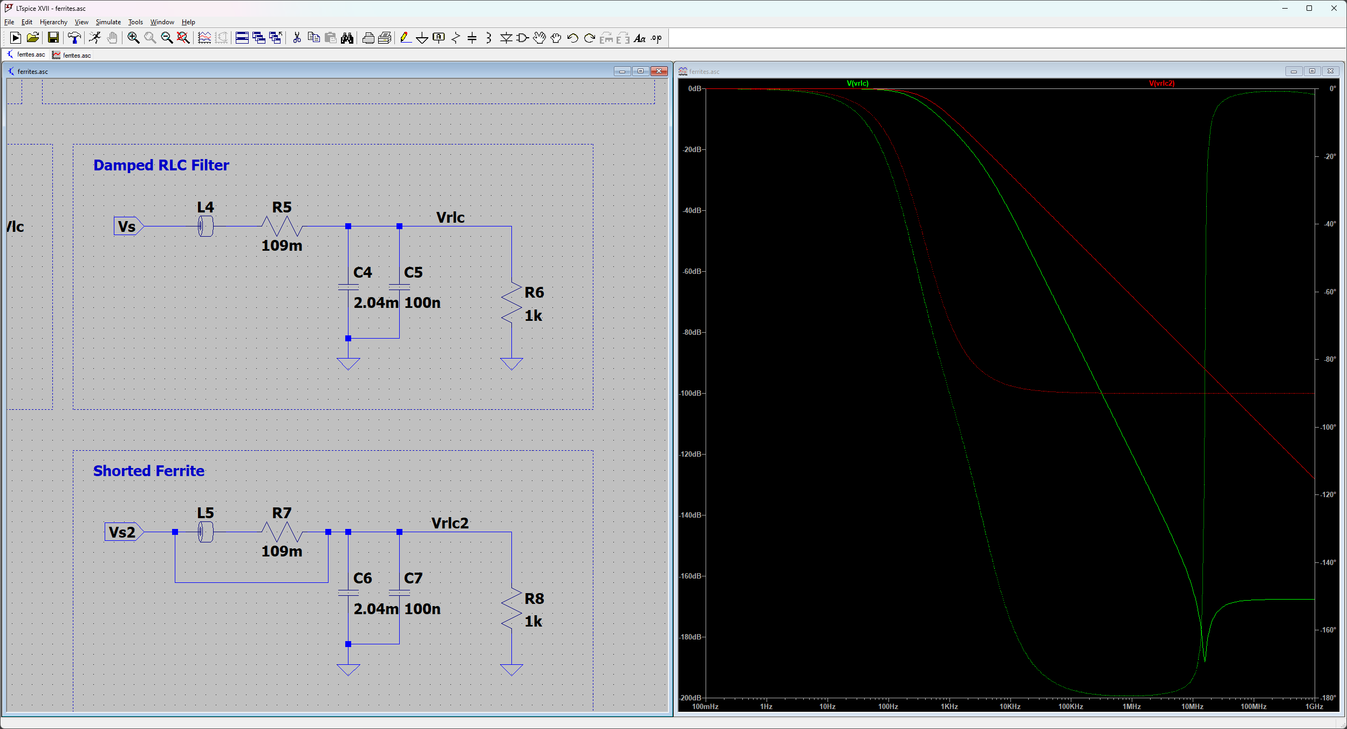
docs/images/Pasted image 20231121190456.png
