JamesNZL/algovision/docs/images/Pasted image 20231121191229.png

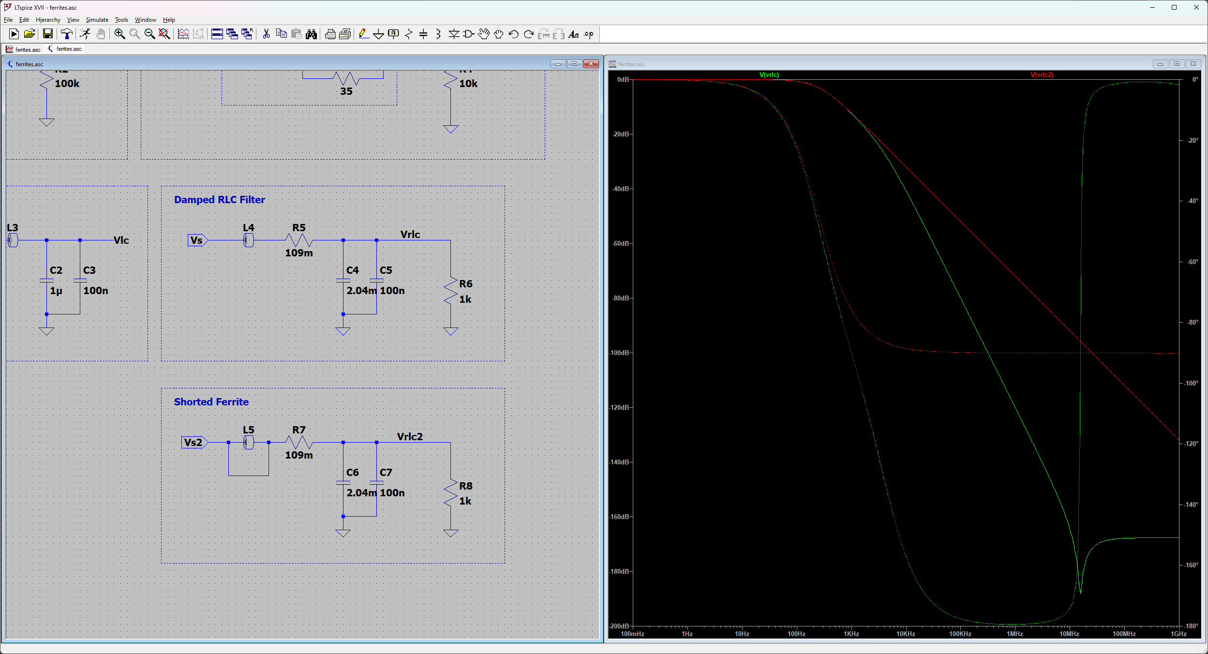
docs/images/Pasted image 20231121191229.png
