JamesNZL/algovision/docs/images/Pasted image 20231121231756.png

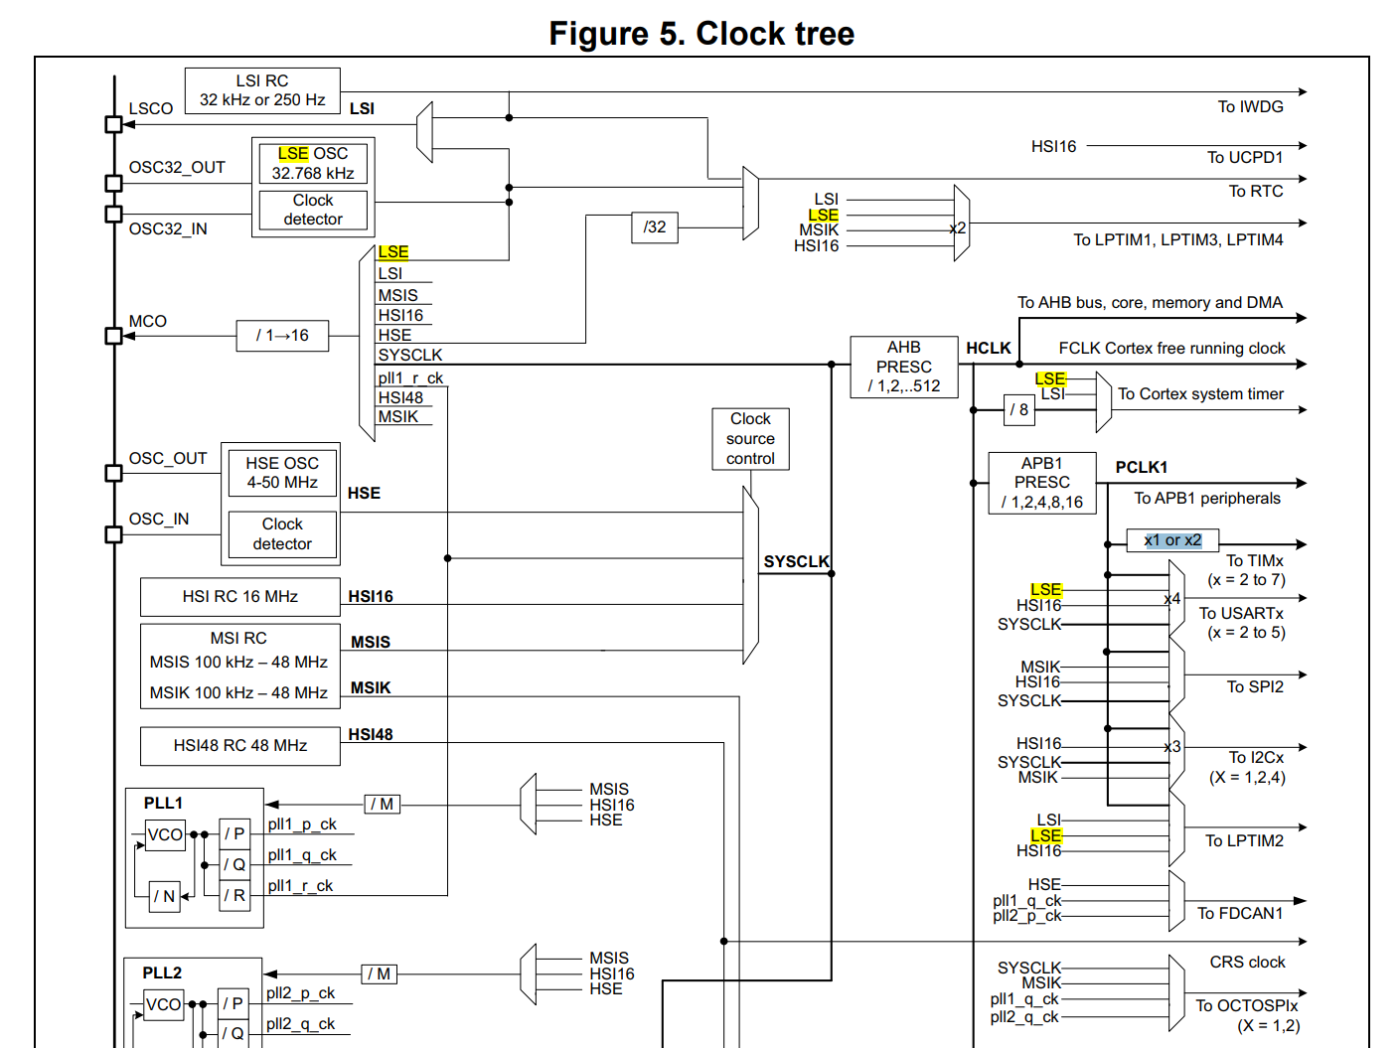
docs/images/Pasted image 20231121231756.png
